sepios87/Projet-Luxi/MatlabLampeI/encodeur.jpg

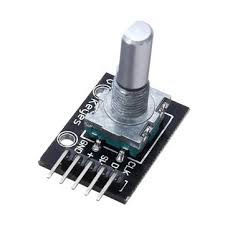
MatlabLampeI/encodeur.jpg
