sepios87/Projet-Luxi/MatlabLampeI/ILS.png

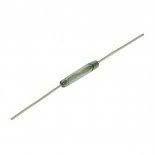
MatlabLampeI/ILS.png
