sepios87/Projet-Luxi/MatlabLampeI/led.jpg

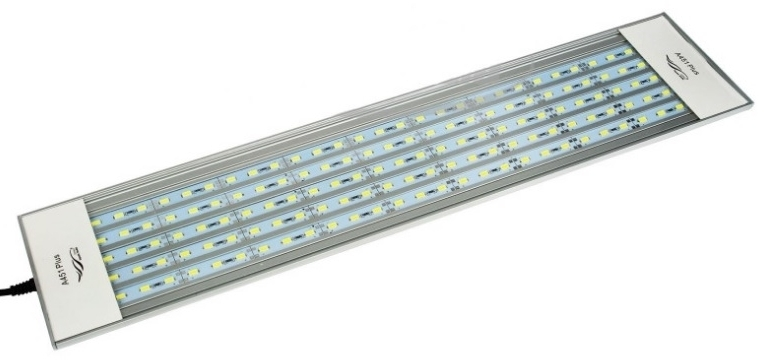
MatlabLampeI/led.jpg
