sepios87/Projet-Luxi/MatlabLampeI/loivitesses.png

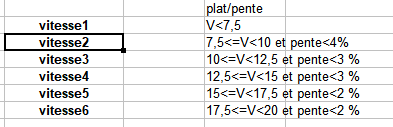
MatlabLampeI/loivitesses.png
