sepios87/Projet-Luxi/MatlabLampeI/pololuM.png

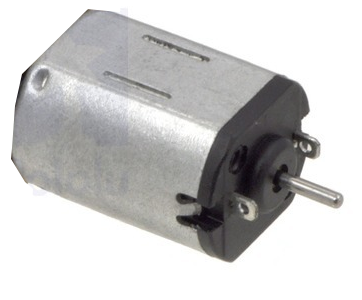
MatlabLampeI/pololuM.png
