sepios87/Projet-Luxi/MatlabLampeI/poulie.png

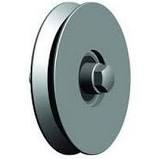
MatlabLampeI/poulie.png
