sepios87/Projet-Luxi/MatlabLampeI/reducpolo.png

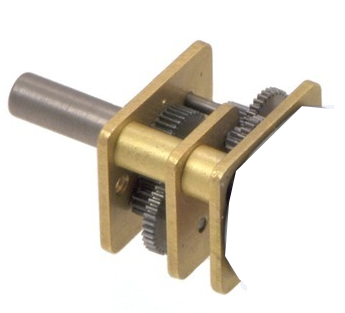
MatlabLampeI/reducpolo.png
