sepios87/Projet-Luxi/MatlabLampeI/roue.png

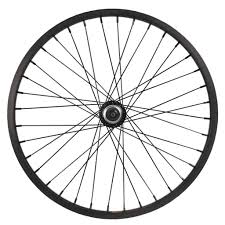
MatlabLampeI/roue.png
