sepios87/Projet-Luxi/MatlabLampeI/VisEcrou.JPG

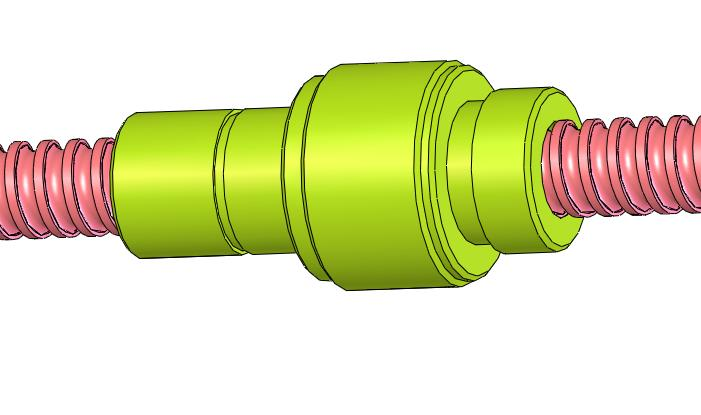
MatlabLampeI/VisEcrou.JPG
